falsonix/DIY-Rudder-Pedals/cad/printable/axle-2x.stl

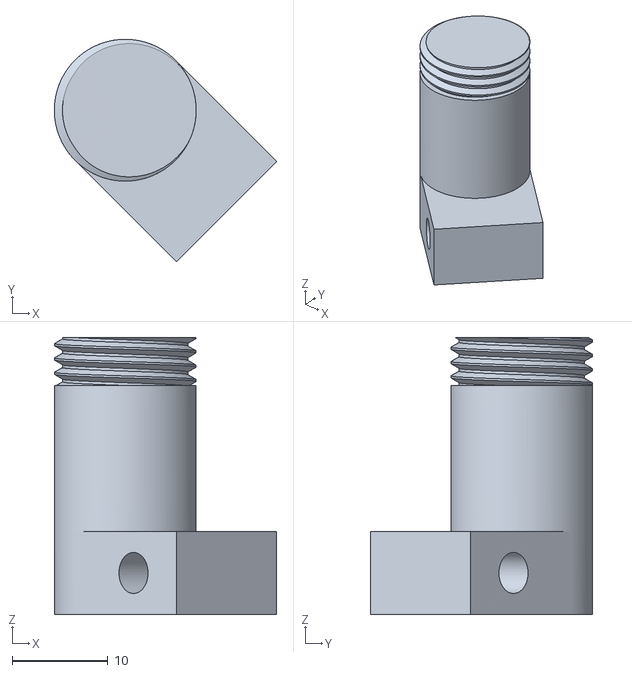
[picture p15: CAD file, 2025-06-16]
cad/printable/axle-2x.stl
23.3 x 23.3 x 29.0
