falsonix/DIY-Rudder-Pedals/cad/printable/pedal-endcap-2x.stl

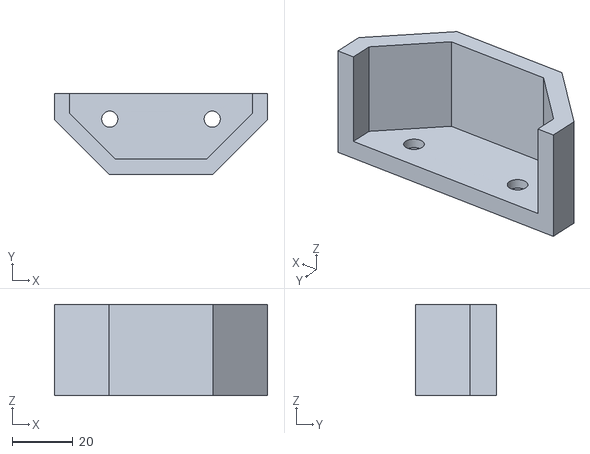
[picture p16: CAD file, 2025-06-16]
cad/printable/pedal-endcap-2x.stl
70.0 x 26.6 x 30.0
